joshbrew/PunyPi/AM625_Chiplet_Altium/Simulation/DDR_Results_Dec-3-2023_15h-55m/DRV_Waveforms_Typ/net-DDR_A10_drv-U1.R5_W1.csv

.HEADER
..NAMES
Time | V U1.R5
.DATA
0.0e+00 | 1.1999
2.33e-11 | 1.1999
4.65e-11 | 1.1999
6.98e-11 | 1.1999
9.31e-11 | 1.1999
1.163e-10 | 1.1999
1.396e-10 | 1.1999
1.629e-10 | 1.1689
1.861e-10 | 1.1131
2.094e-10 | 0.9578
2.327e-10 | 0.8072
2.559e-10 | 0.7068
2.792e-10 | 0.6438
3.025e-10 | 0.6029
3.257e-10 | 0.5752
3.490e-10 | 0.5559
3.723e-10 | 0.5402
3.955e-10 | 0.5279
4.188e-10 | 0.5179
4.421e-10 | 0.5102
4.653e-10 | 0.5050
4.886e-10 | 0.5028
5.119e-10 | 0.5035
5.351e-10 | 0.5078
5.584e-10 | 0.5127
5.817e-10 | 0.5159
6.049e-10 | 0.5139
6.282e-10 | 0.5053
6.515e-10 | 0.4906
6.747e-10 | 0.4684
6.980e-10 | 0.4339
7.213e-10 | 0.3818
7.445e-10 | 0.3132
7.678e-10 | 0.2359
7.911e-10 | 0.1602
8.143e-10 | 0.0956
8.376e-10 | 0.0477
8.609e-10 | 0.0165
8.841e-10 | -0.0019
9.074e-10 | -0.0135
9.307e-10 | -0.0234
9.539e-10 | -0.0340
9.772e-10 | -0.0454
1.0005e-09 | -0.0569
1.0237e-09 | -0.0678
1.0470e-09 | -0.0771
1.0703e-09 | -0.0831
1.0935e-09 | -0.0838
1.1168e-09 | -0.0779
1.1401e-09 | -0.0663
1.1633e-09 | -0.0513
1.1866e-09 | -0.0348
1.2099e-09 | -0.0169
1.2332e-09 | 0.0030
1.2564e-09 | 0.0240
1.2797e-09 | 0.0440
1.3030e-09 | 0.0596
1.3262e-09 | 0.0677
1.3495e-09 | 0.0667
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
