joshbrew/PunyPi/AM625_Chiplet_Altium/Simulation/DDR_Results_Dec-3-2023_15h-55m/DRV_Waveforms_Typ/net-DDR_A12_drv-U1.R6_W1.csv

.HEADER
..NAMES
Time | V U1.R6
.DATA
0.0e+00 | 0.0027
2.33e-11 | 0.0027
4.65e-11 | 0.0027
6.98e-11 | 0.0027
9.31e-11 | 0.0027
1.163e-10 | 0.0027
1.396e-10 | 0.0027
1.629e-10 | 0.0059
1.861e-10 | 0.0318
2.094e-10 | 0.1119
2.327e-10 | 0.2668
2.559e-10 | 0.3828
2.792e-10 | 0.4673
3.025e-10 | 0.5264
3.257e-10 | 0.5661
3.490e-10 | 0.5922
3.723e-10 | 0.6113
3.955e-10 | 0.6263
4.188e-10 | 0.6394
4.421e-10 | 0.6494
4.653e-10 | 0.6572
4.886e-10 | 0.6625
5.119e-10 | 0.6662
5.351e-10 | 0.6678
5.584e-10 | 0.6667
5.817e-10 | 0.6629
6.049e-10 | 0.6588
6.282e-10 | 0.6582
6.515e-10 | 0.6639
6.747e-10 | 0.6774
6.980e-10 | 0.7006
7.213e-10 | 0.7381
7.445e-10 | 0.7942
7.678e-10 | 0.8661
7.911e-10 | 0.9448
8.143e-10 | 1.0194
8.376e-10 | 1.0805
8.609e-10 | 1.1244
8.841e-10 | 1.1530
9.074e-10 | 1.1714
9.307e-10 | 1.1851
9.539e-10 | 1.1983
9.772e-10 | 1.2123
1.0005e-09 | 1.2259
1.0237e-09 | 1.2371
1.0470e-09 | 1.2449
1.0703e-09 | 1.2502
1.0935e-09 | 1.2539
1.1168e-09 | 1.2551
1.1401e-09 | 1.2519
1.1633e-09 | 1.2433
1.1866e-09 | 1.2300
1.2099e-09 | 1.2134
1.2332e-09 | 1.1942
1.2564e-09 | 1.1733
1.2797e-09 | 1.1526
1.3030e-09 | 1.1352
1.3262e-09 | 1.1246
1.3495e-09 | 1.1229
1.3728e-09 | 1.1299
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
